RodrigoFass/rig-camcorder-vcc4344/mesas/2_berco_tampa_PETG.3mf

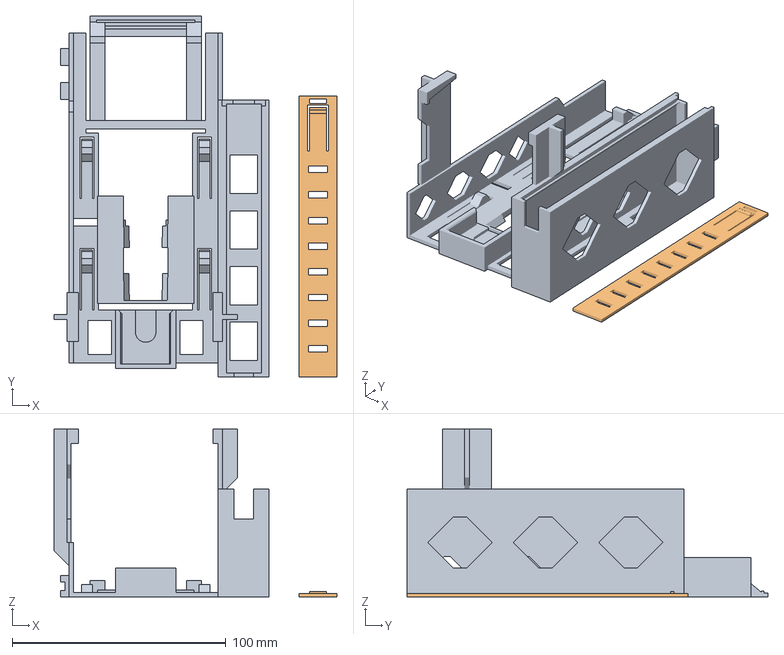
[picture p24: CAD file, 2026-10-07]
mesas/2_berco_tampa_PETG.3mf
132.4 x 168.9 x 78.4 mm
PETG - berco
PETG - tampa_caixa_easycap
