RodrigoFass/rig-camcorder-vcc4344/stl/cabo.stl

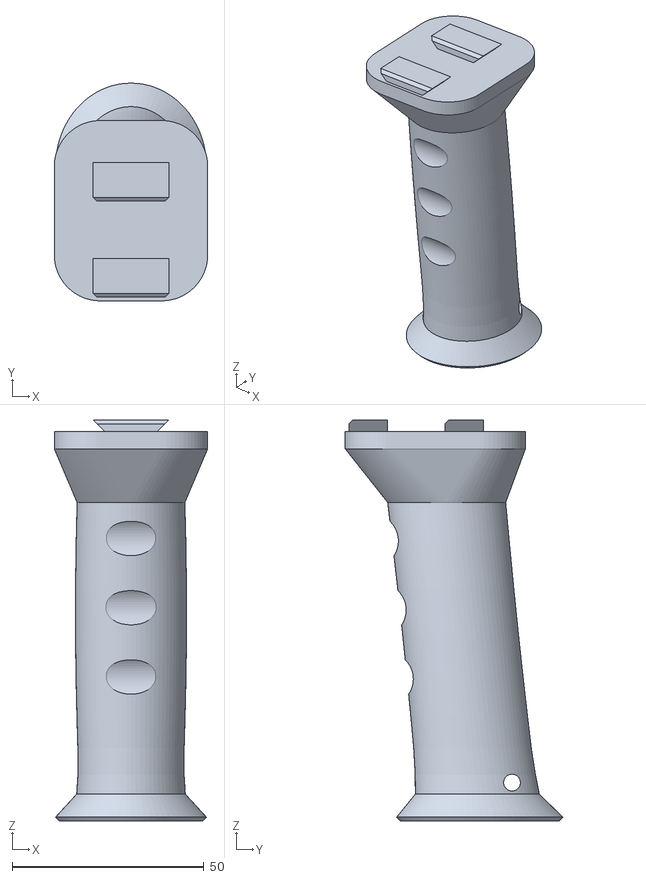
[picture p25: CAD file, 2026-10-07]
stl/cabo.stl
40.0 x 56.8 x 104.5
