RodrigoFass/rig-camcorder-vcc4344/stl/garra.stl

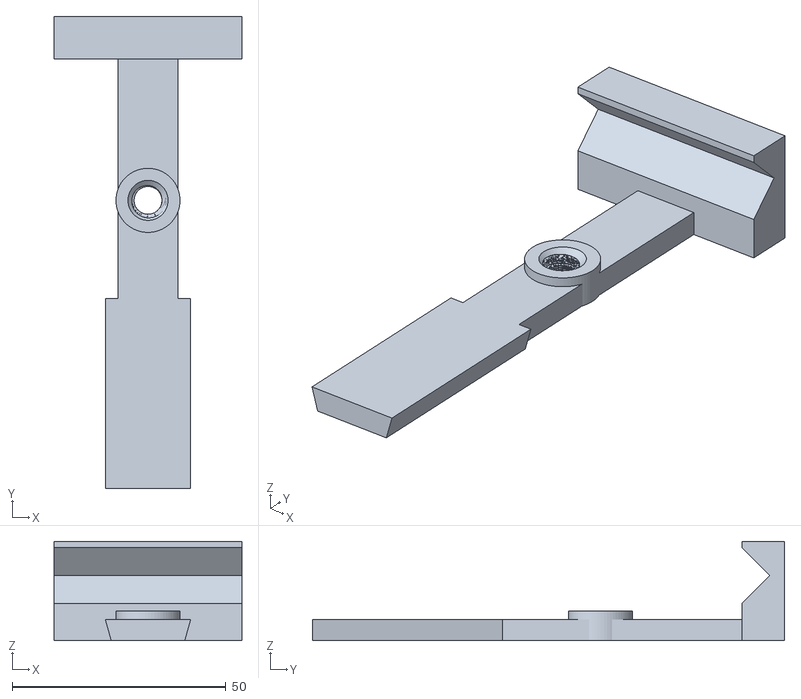
[picture p26: CAD file, 2026-10-07]
stl/garra.stl
44.0 x 110.5 x 23.2
