RodrigoFass/rig-camcorder-vcc4344/stl/trava_celular.stl

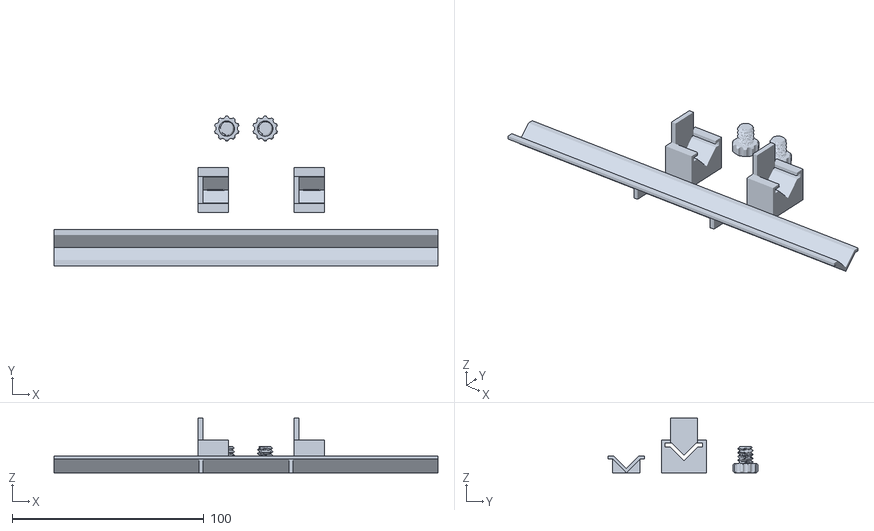
[picture p27: CAD file, 2026-10-07]
stl/trava_celular.stl
200.0 x 78.0 x 28.5
