RodrigoFass/rig-camcorder-vcc4344/stl/trava_ponte.stl

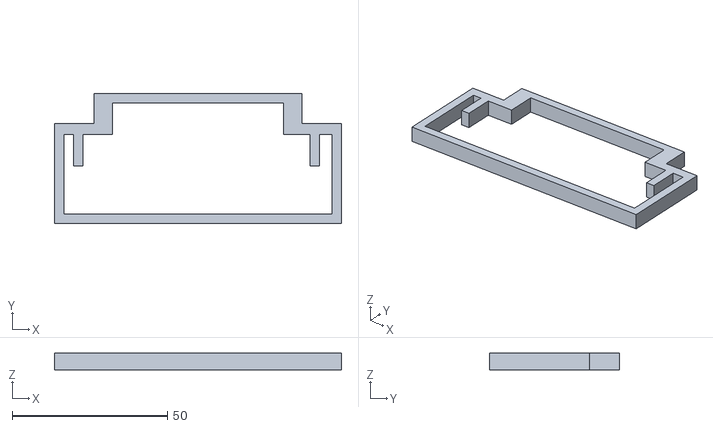
[picture p28: CAD file, 2026-10-07]
stl/trava_ponte.stl
92.4 x 41.7 x 5.35
