RodrigoFass/rig-camcorder-vcc4344/stl/garfo.stl

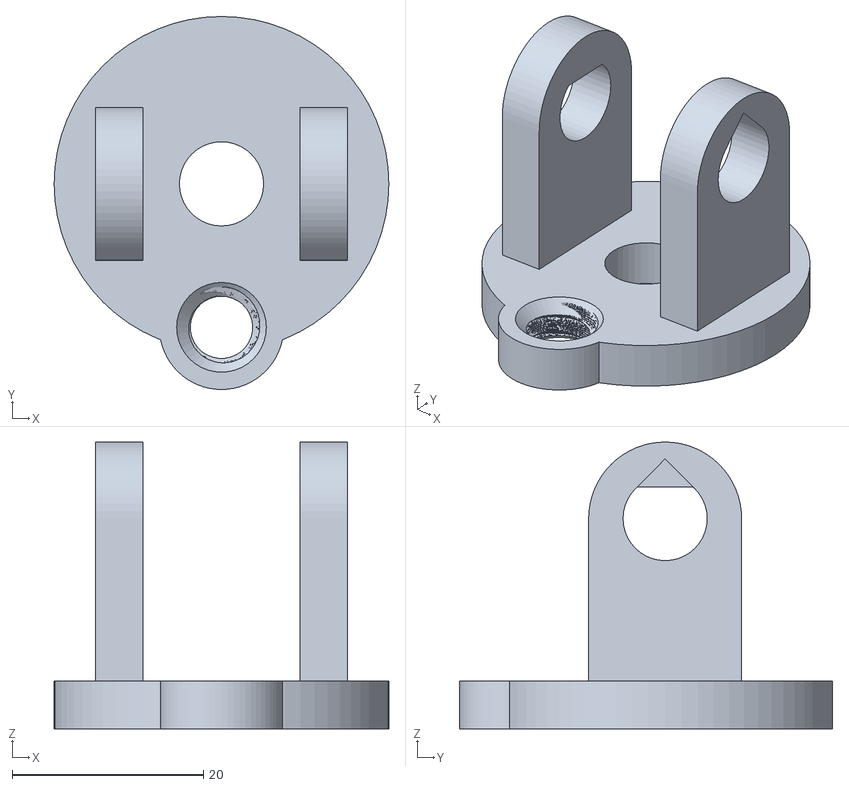
[picture p29: CAD file, 2026-10-07]
stl/garfo.stl
35.0 x 39.0 x 30.0
