RodrigoFass/rig-camcorder-vcc4344/stl/topo.stl

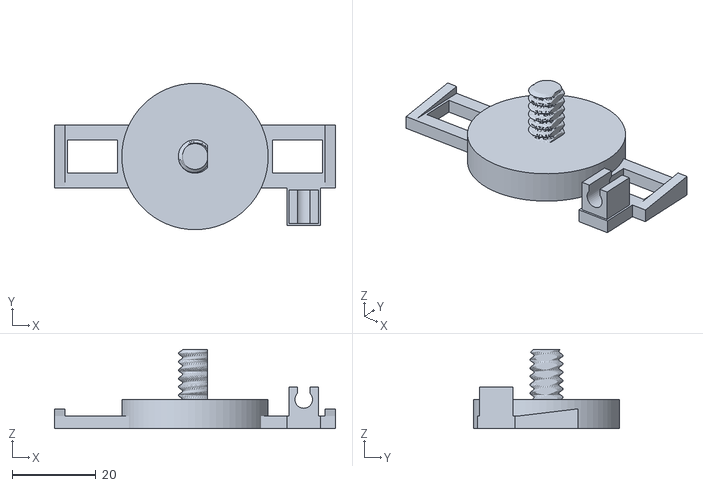
[picture p30: CAD file, 2026-10-07]
stl/topo.stl
67.2 x 35.0 x 19.0
