RodrigoFass/rig-camcorder-vcc4344/stl/testes_petg.stl

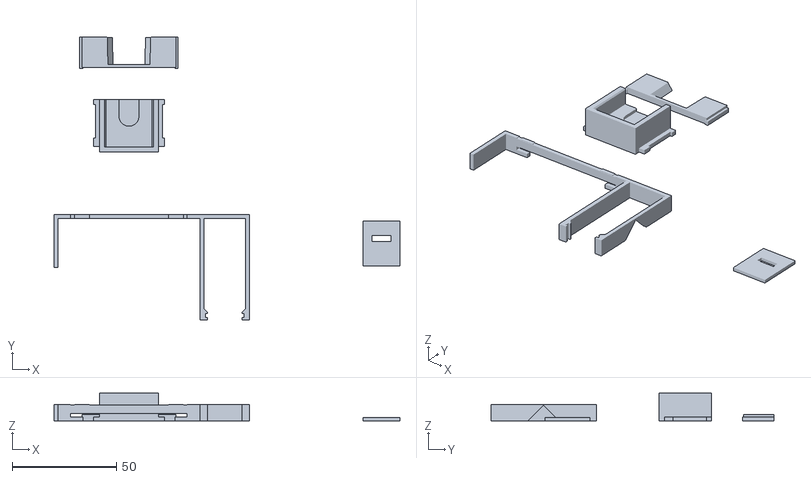
[picture p31: CAD file, 2026-10-07]
stl/testes_petg.stl
165.7 x 135.5 x 13.4
